sebgad/CoffeeControl/ota.h

// generated with command: 
//  gzip ota.html
//  hexdump --format '15/1 "0x%.2x,""\n"' ota.html.gz
// file size: wc -c ota.html.gz
#define ota_html_gz_len 730
const uint8_t ota_html_gz[] PROGMEM = {
  0x1F,0x8B,0x08,0x08,0x94,0x7C,0x01,0x62,0x00,0x03,0x6F,0x74,0x61,0x2E,0x68,
  0x74,0x6D,0x6C,0x00,0xAD,0x55,0x4D,0x6F,0xE3,0x46,0x0C,0xBD,0xE7,0x57,0xB0,
  0xD3,0x6B,0x65,0x6D,0xBC,0x08,0xB0,0x70,0x25,0x01,0x69,0xD2,0xB4,0x97,0x22,
  0x8B,0x26,0x39,0xF4,0x54,0x50,0x12,0x65,0xB1,0x19,0xCD,0x0C,0x34,0x23,0xC7,
  0x6E,0xB1,0xFF,0xBD,0x1C,0x7D,0x64,0xB3,0xAA,0x81,0x76,0x81,0xC2,0xB0,0x25,
  0x92,0x8F,0x8F,0xE4,0x9B,0x0F,0x67,0xDF,0xDC,0xDE,0xDF,0x3C,0xFE,0xF6,0xF1,
  0x47,0x68,0x43,0xA7,0x8B,0x8B,0x2C,0x3E,0x40,0xA3,0xD9,0xE7,0x8A,0x8C,0x8A,
  0x0E,0xC2,0xBA,0xB8,0x00,0xC8,0x34,0x9B,0x67,0xE8,0x49,0xE7,0xCA,0x87,0x93,
  0x26,0xDF,0x12,0x05,0x05,0xE1,0xE4,0x28,0x57,0x81,0x8E,0x21,0xAD,0xBC,0x57,
  0xD0,0xF6,0xD4,0xCC,0x88,0x4D,0x74,0xAC,0x52,0xD1,0x39,0x4D,0x49,0xB0,0x43,
  0xD5,0x26,0x5C,0x59,0xA3,0xC0,0xF3,0x9F,0xE4,0x73,0x75,0xF9,0xE1,0xDD,0x51,
  0xBE,0x0B,0x41,0xBA,0x06,0x6E,0x9C,0xD9,0xAF,0xC9,0x26,0x82,0xA9,0x03,0xEE,
  0x70,0x4F,0x69,0x04,0x2D,0x8C,0xEF,0xB7,0xC7,0xF7,0xDB,0x57,0xBE,0x06,0x0F,
  0x11,0x9E,0x8C,0xDE,0xCF,0x64,0x81,0x83,0xA6,0xE2,0x07,0x34,0xF2,0xB9,0xB1,
  0x4D,0x43,0x94,0xA5,0x93,0x2F,0x46,0x3B,0x0A,0x08,0x55,0x8B,0xBD,0xA7,0x90,
  0xAB,0xA7,0xC7,0xBB,0xE4,0x83,0xFA,0x1C,0x30,0xD8,0x49,0xE1,0x03,0xD3,0x8B,
  0xB3,0xBD,0x48,0x21,0xF4,0x81,0x8C,0x00,0x5F,0xB8,0x0E,0x6D,0x5E,0x93,0x54,
  0xA4,0x64,0x34,0xBE,0x03,0x36,0x1C,0x18,0x75,0xE2,0x2B,0xD4,0x94,0x5F,0x46,
  0x65,0xD3,0x49,0xDA,0xAC,0xB4,0xF5,0x69,0x64,0x1D,0x55,0x8B,0x6F,0x00,0x0E,
  0xFE,0x1A,0x9F,0x00,0x35,0x7B,0xA7,0xF1,0xB4,0x83,0x46,0xD3,0xF1,0xFB,0xD9,
  0xF9,0xC7,0xE0,0x03,0x37,0xA7,0x64,0x2E,0xB9,0x03,0x4D,0x4D,0x58,0x82,0xA8,
  0x79,0x6F,0x12,0x0E,0xD4,0xF9,0x1D,0x54,0x12,0xA6,0x7E,0x0A,0x7D,0xBA,0x98,
  0xB9,0x0B,0xF0,0x0E,0xCD,0x3F,0x4B,0xB0,0x11,0x71,0x29,0x29,0xB5,0xAD,0x9E,
  0x17,0xB6,0xB1,0xFF,0x1D,0x6C,0xDF,0xB9,0xE3,0x59,0x96,0x5D,0xC3,0xBD,0x0F,
  0x49,0xD5,0xB2,0xAE,0xBF,0x92,0xF1,0x0D,0x65,0xFC,0xCD,0xD2,0x59,0x80,0x8B,
  0xAC,0xE6,0x03,0x54,0x1A,0xBD,0x2C,0x63,0x14,0x89,0xFA,0x49,0xF6,0xF6,0x72,
  0xB5,0x54,0xE2,0x10,0xFF,0xB5,0x2C,0x79,0x27,0xDB,0x05,0xB2,0xB2,0x78,0xA1,
  0x52,0x8A,0xCA,0xC8,0x0D,0x56,0x02,0x28,0x0B,0x08,0x76,0x5C,0x99,0xDE,0x6A,
  0xF8,0x15,0x4D,0xC5,0x9A,0x2D,0x3C,0xB0,0x3E,0x30,0x02,0x79,0xD7,0x93,0xF7,
  0x16,0x3A,0x94,0xFE,0x0D,0x6D,0x64,0x51,0xA4,0xF4,0xAA,0x03,0x83,0x87,0x12,
  0xE7,0x0E,0x70,0xD9,0x4F,0xAA,0xF8,0xD9,0x76,0x52,0x00,0xBF,0x70,0xEF,0x7B,
  0x74,0xAD,0xDF,0xC4,0x43,0xA4,0x8A,0x9F,0x46,0x63,0x0D,0x91,0xAD,0x14,0xD8,
  0xEC,0x17,0xD0,0xC3,0x6C,0xAE,0x61,0x36,0xE0,0x84,0x58,0xBA,0xC0,0x2A,0xF0,
  0x81,0x54,0x71,0xFF,0x78,0xBD,0xC6,0x7E,0xFB,0x0A,0xEA,0x79,0xDF,0x06,0x55,
  0x5C,0x97,0x76,0x08,0x23,0xEA,0xDC,0x3C,0x1D,0xB2,0x99,0xF5,0xDC,0x16,0x77,
  0xDC,0x77,0x2F,0xD8,0x13,0x3C,0xB9,0x1A,0x43,0x94,0x74,0x3B,0x86,0x1A,0xDB,
  0x77,0x20,0xDB,0xBC,0xB5,0x75,0xAE,0x3E,0xDE,0x3F,0x3C,0x2A,0x88,0x1D,0x58,
  0x23,0xB3,0x4B,0x6F,0xBF,0x37,0x73,0x9E,0x02,0x32,0xD5,0x74,0x04,0xBB,0x41,
  0x07,0x76,0xD8,0x87,0x34,0x26,0x27,0x42,0x87,0x31,0xA9,0x22,0x17,0xCE,0x9C,
  0xA1,0x78,0x92,0xB1,0x24,0x5D,0xFC,0x72,0x7B,0x05,0x37,0x2D,0x55,0xCF,0x7E,
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
};
